realizator/stereopi-kicad-schematic/Output/StereoPi_Main-Main.pdf

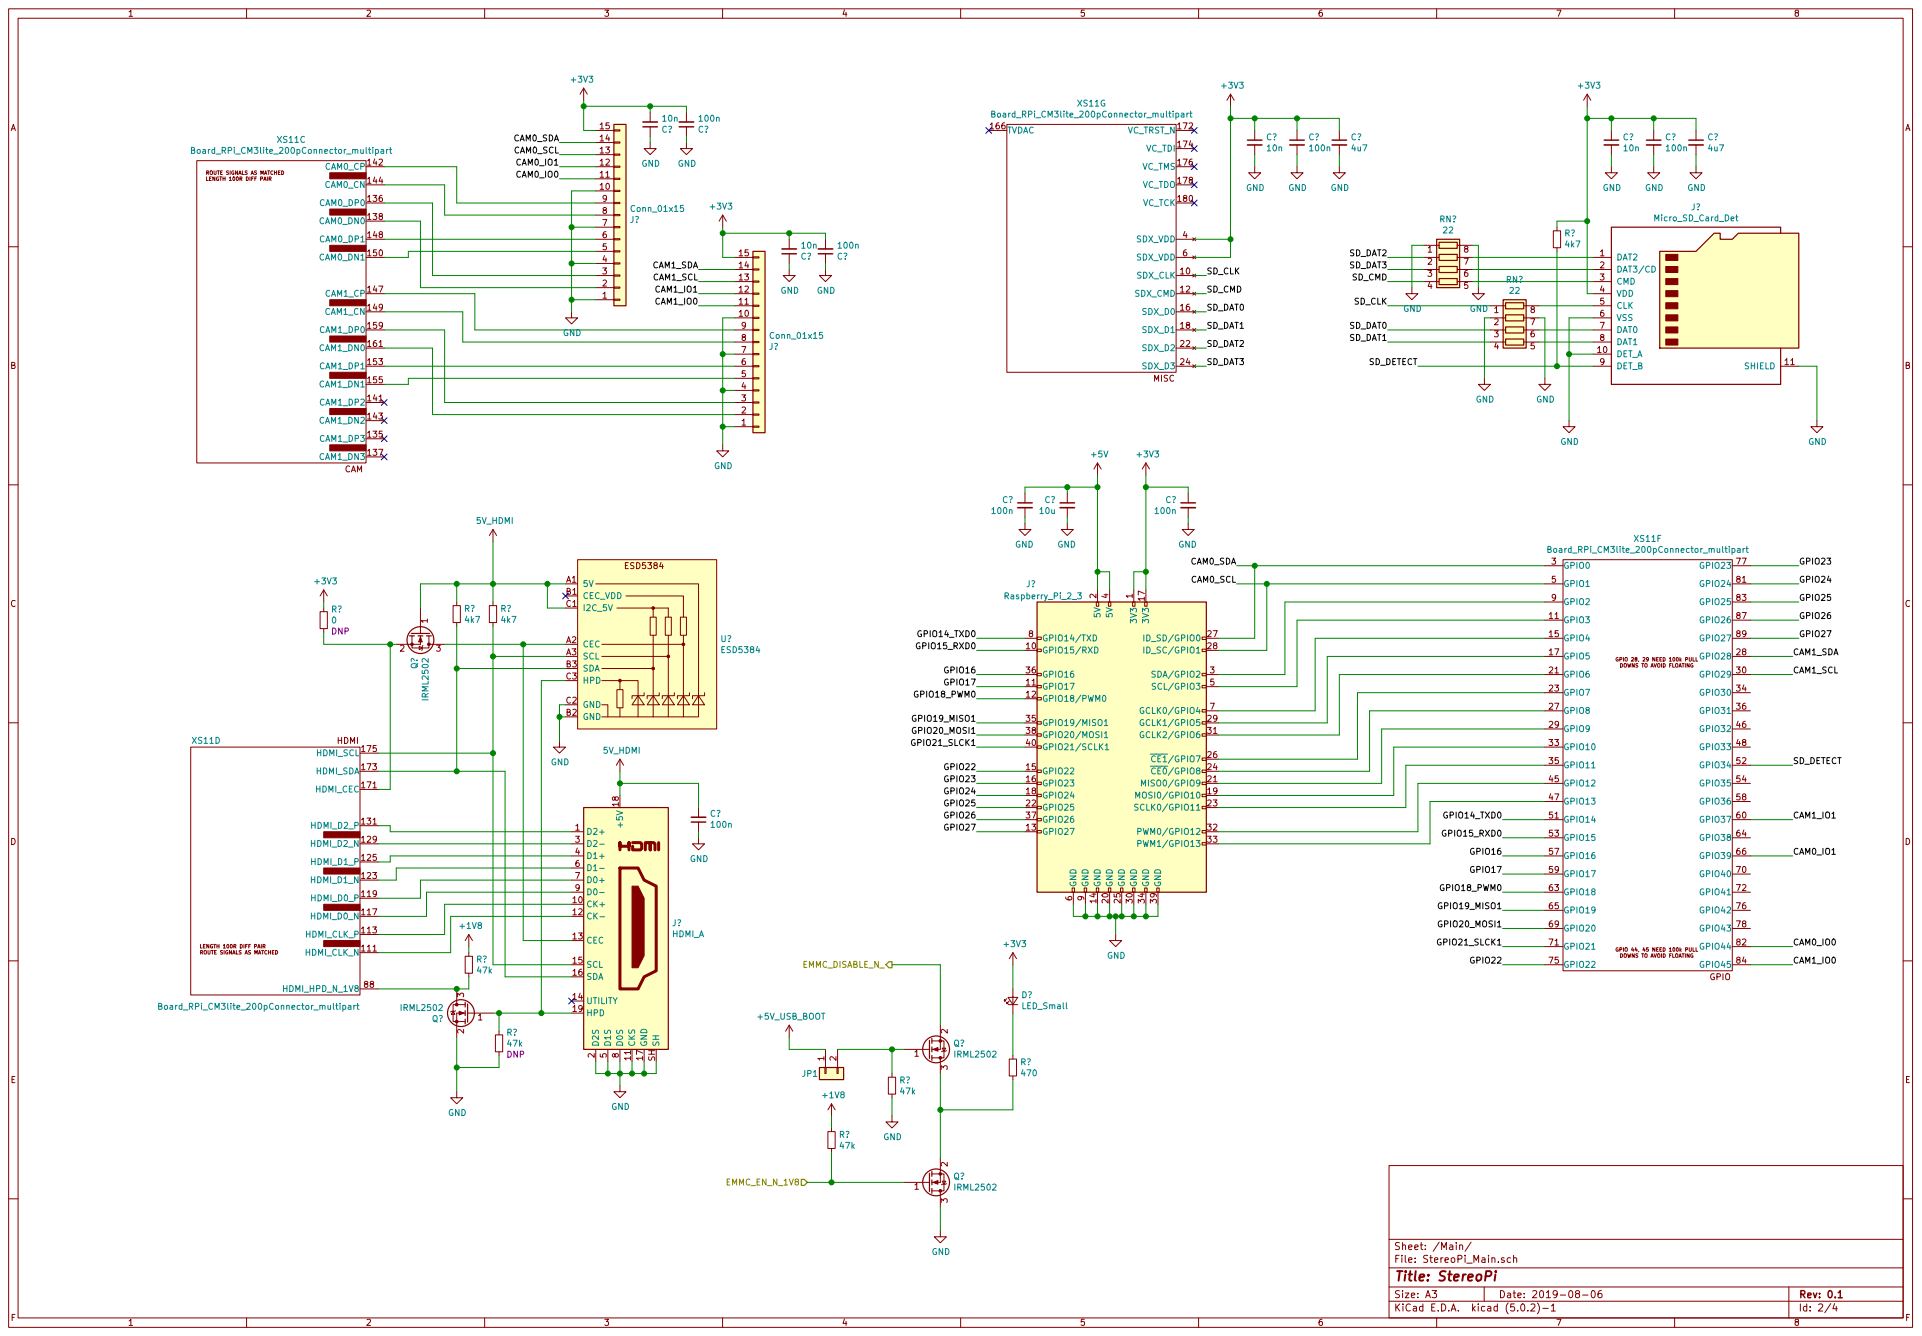
[picture p10: page 1]

Board_RPi_CM3lite_200pConnector_multipart HDMI LENGTH 100R DIFF PAIR

DOWNS TO AVOID FLOATING

File: StereoPi_Main.sch Sheet: /Main/
Id: 2/4 Title: StereoPi
