realizator/stereopi-kicad-schematic/Output/StereoPiFootprints.pdf

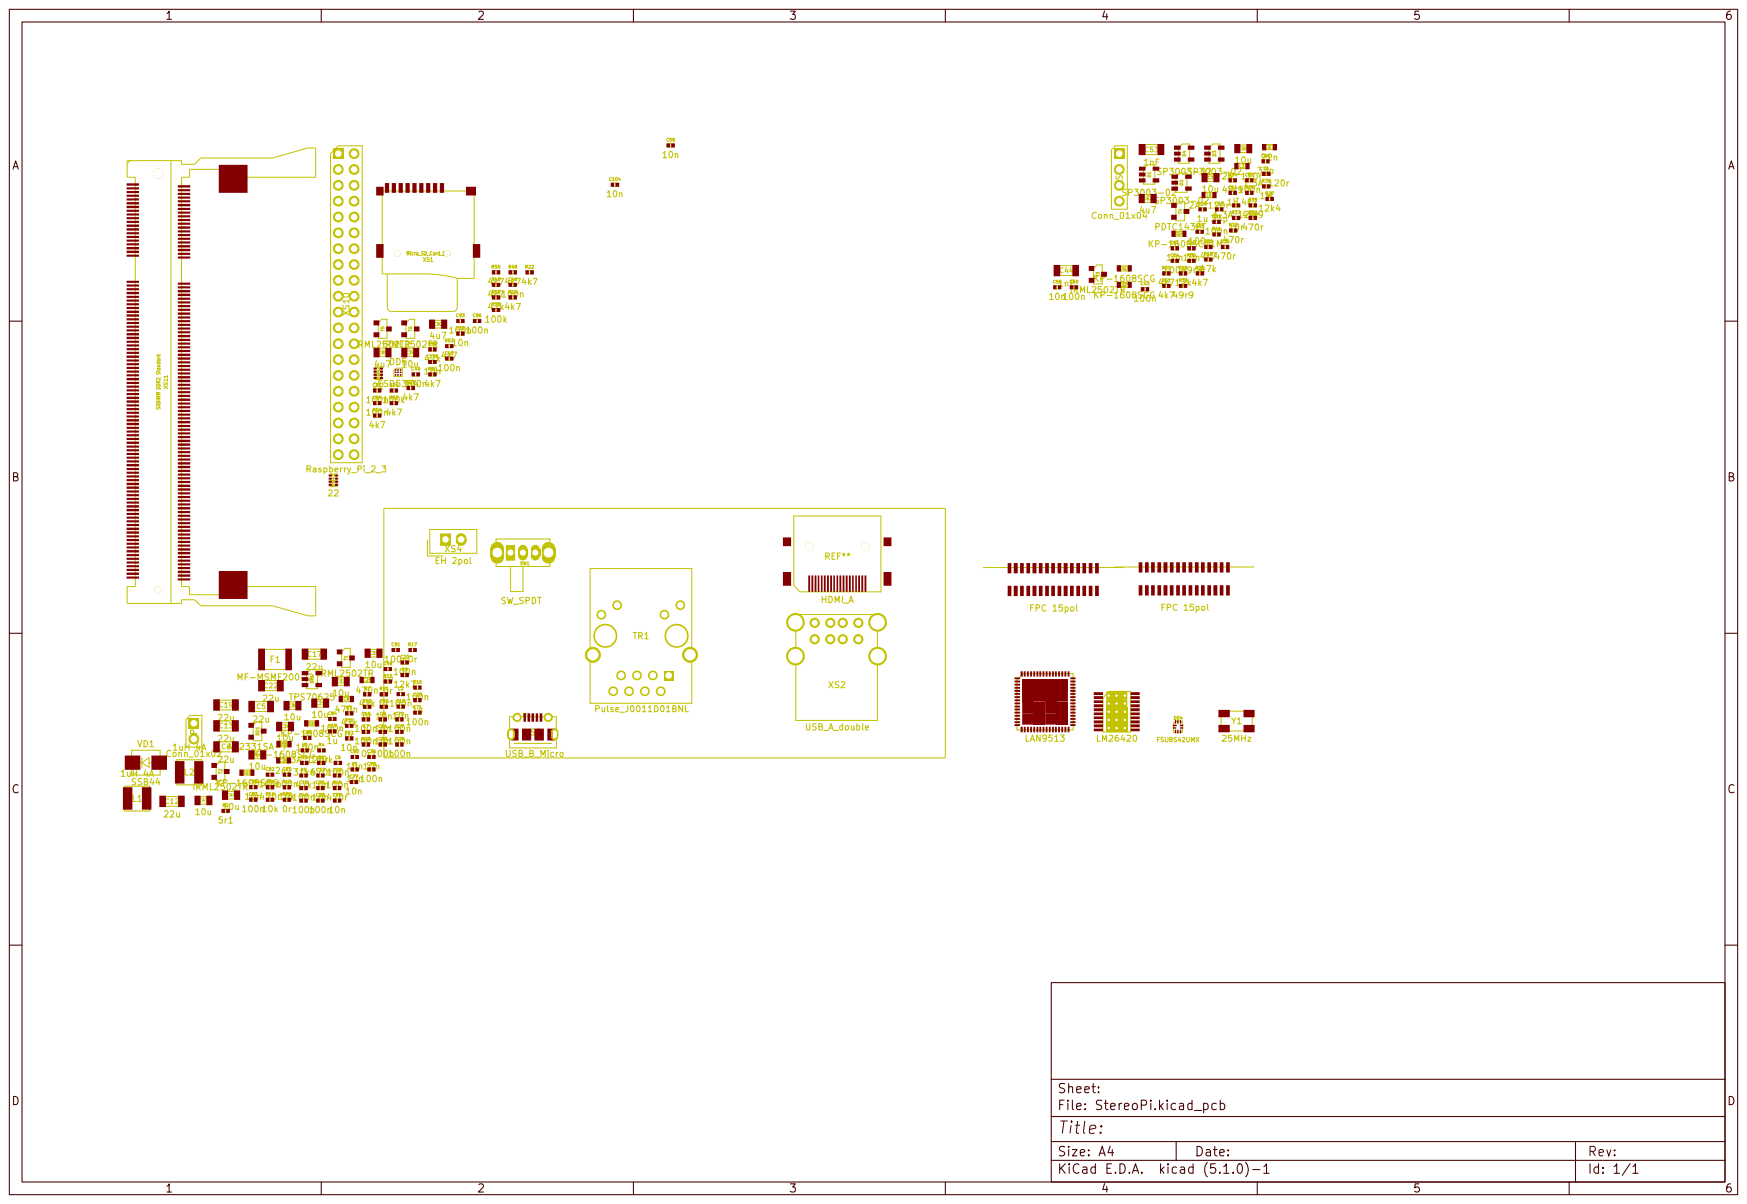
[picture p17: page 1]
